bablokb/pcb-pico-pi-base/circuitpython/esp32s3_zero_base_rev1/pins.c

#include "shared-bindings/board/__init__.h"

STATIC const mp_rom_map_elem_t board_module_globals_table[] = {
    CIRCUITPYTHON_BOARD_DICT_STANDARD_ITEMS

    { MP_ROM_QSTR(MP_QSTR_GP0), MP_ROM_PTR(&pin_GPIO11) },
    { MP_ROM_QSTR(MP_QSTR_GP1), MP_ROM_PTR(&pin_GPIO12) },
    { MP_ROM_QSTR(MP_QSTR_GP2), MP_ROM_PTR(&pin_GPIO13) },
    { MP_ROM_QSTR(MP_QSTR_GP3), MP_ROM_PTR(&pin_GPIO14) },
    { MP_ROM_QSTR(MP_QSTR_GP4), MP_ROM_PTR(&pin_GPIO15) },
    { MP_ROM_QSTR(MP_QSTR_GP5), MP_ROM_PTR(&pin_GPIO16) },
    { MP_ROM_QSTR(MP_QSTR_GP6), MP_ROM_PTR(&pin_GPIO17) },
    { MP_ROM_QSTR(MP_QSTR_GP7), MP_ROM_PTR(&pin_GPIO18) },
    { MP_ROM_QSTR(MP_QSTR_GP8), MP_ROM_PTR(&pin_GPIO33) },
    { MP_ROM_QSTR(MP_QSTR_GP9), MP_ROM_PTR(&pin_GPIO34) },
    { MP_ROM_QSTR(MP_QSTR_GP10), MP_ROM_PTR(&pin_GPIO35) },
    { MP_ROM_QSTR(MP_QSTR_GP11), MP_ROM_PTR(&pin_GPIO36) },
    { MP_ROM_QSTR(MP_QSTR_GP12), MP_ROM_PTR(&pin_GPIO37) },
    { MP_ROM_QSTR(MP_QSTR_GP13), MP_ROM_PTR(&pin_GPIO38) },
    { MP_ROM_QSTR(MP_QSTR_GP14), MP_ROM_PTR(&pin_GPIO39) },
    { MP_ROM_QSTR(MP_QSTR_GP15), MP_ROM_PTR(&pin_GPIO40) },
    { MP_ROM_QSTR(MP_QSTR_GP16), MP_ROM_PTR(&pin_GPIO42) },
    { MP_ROM_QSTR(MP_QSTR_GP17), MP_ROM_PTR(&pin_GPIO41) },
    { MP_ROM_QSTR(MP_QSTR_GP18), MP_ROM_PTR(&pin_GPIO1) },
    { MP_ROM_QSTR(MP_QSTR_GP19), MP_ROM_PTR(&pin_GPIO2) },
    { MP_ROM_QSTR(MP_QSTR_GP20), MP_ROM_PTR(&pin_GPIO4) },
    { MP_ROM_QSTR(MP_QSTR_GP21), MP_ROM_PTR(&pin_GPIO5) },
    { MP_ROM_QSTR(MP_QSTR_GP22), MP_ROM_PTR(&pin_GPIO6) },
    { MP_ROM_QSTR(MP_QSTR_GP26), MP_ROM_PTR(&pin_GPIO7) },
    { MP_ROM_QSTR(MP_QSTR_GP27), MP_ROM_PTR(&pin_GPIO8) },
    { MP_ROM_QSTR(MP_QSTR_GP28), MP_ROM_PTR(&pin_GPIO9) },

    { MP_ROM_QSTR(MP_QSTR_GPIO2), MP_ROM_PTR(&pin_GPIO13) },
    { MP_ROM_QSTR(MP_QSTR_SDA),   MP_ROM_PTR(&pin_GPIO13) },

    { MP_ROM_QSTR(MP_QSTR_GPIO3), MP_ROM_PTR(&pin_GPIO14) },
    { MP_ROM_QSTR(MP_QSTR_SCL),   MP_ROM_PTR(&pin_GPIO14) },

    { MP_ROM_QSTR(MP_QSTR_GPIO4), MP_ROM_PTR(&pin_GPIO15) },
    { MP_ROM_QSTR(MP_QSTR_GPIO5), MP_ROM_PTR(&pin_GPIO5) },
    { MP_ROM_QSTR(MP_QSTR_GPIO6), MP_ROM_PTR(&pin_GPIO38) },

    { MP_ROM_QSTR(MP_QSTR_GPIO7), MP_ROM_PTR(&pin_GPIO6) },
    { MP_ROM_QSTR(MP_QSTR_CE1),   MP_ROM_PTR(&pin_GPIO6) },

    { MP_ROM_QSTR(MP_QSTR_GPIO8),  MP_ROM_PTR(&pin_GPIO34) },
    { MP_ROM_QSTR(MP_QSTR_CE0),    MP_ROM_PTR(&pin_GPIO34) },

    { MP_ROM_QSTR(MP_QSTR_GPIO9), MP_ROM_PTR(&pin_GPIO37) },
    { MP_ROM_QSTR(MP_QSTR_MISO),  MP_ROM_PTR(&pin_GPIO37) },

    { MP_ROM_QSTR(MP_QSTR_GPIO10), MP_ROM_PTR(&pin_GPIO36) },
    { MP_ROM_QSTR(MP_QSTR_MOSI),   MP_ROM_PTR(&pin_GPIO36) },

    { MP_ROM_QSTR(MP_QSTR_GPIO11), MP_ROM_PTR(&pin_GPIO35) },
    { MP_ROM_QSTR(MP_QSTR_SCLK),   MP_ROM_PTR(&pin_GPIO35) },

    { MP_ROM_QSTR(MP_QSTR_GPIO12), MP_ROM_PTR(&pin_GPIO4) },
    { MP_ROM_QSTR(MP_QSTR_GPIO13), MP_ROM_PTR(&pin_GPIO39) },

    { MP_ROM_QSTR(MP_QSTR_GPIO14), MP_ROM_PTR(&pin_GPIO11) },
    { MP_ROM_QSTR(MP_QSTR_TX),    MP_ROM_PTR(&pin_GPIO11) },

    { MP_ROM_QSTR(MP_QSTR_GPIO15), MP_ROM_PTR(&pin_GPIO12) },
    { MP_ROM_QSTR(MP_QSTR_RX),     MP_ROM_PTR(&pin_GPIO12) },

    { MP_ROM_QSTR(MP_QSTR_GPIO23), MP_ROM_PTR(&pin_GPIO33) },

    { MP_ROM_QSTR(MP_QSTR_GPIO16), MP_ROM_PTR(&pin_GPIO41) },
    { MP_ROM_QSTR(MP_QSTR_GPIO17), MP_ROM_PTR(&pin_GPIO16) },
    { MP_ROM_QSTR(MP_QSTR_GPIO18), MP_ROM_PTR(&pin_GPIO9) },

    { MP_ROM_QSTR(MP_QSTR_GPIO19), MP_ROM_PTR(&pin_GPIO42) },
    { MP_ROM_QSTR(MP_QSTR_MISO1),  MP_ROM_PTR(&pin_GPIO42) },

    { MP_ROM_QSTR(MP_QSTR_GPIO20), MP_ROM_PTR(&pin_GPIO2) },
    { MP_ROM_QSTR(MP_QSTR_MOSI1),  MP_ROM_PTR(&pin_GPIO2) },

    { MP_ROM_QSTR(MP_QSTR_GPIO21), MP_ROM_PTR(&pin_GPIO1) },
    { MP_ROM_QSTR(MP_QSTR_SCLK1),  MP_ROM_PTR(&pin_GPIO1) },

    { MP_ROM_QSTR(MP_QSTR_GPIO22), MP_ROM_PTR(&pin_GPIO18) },
    { MP_ROM_QSTR(MP_QSTR_GPIO24), MP_ROM_PTR(&pin_GPIO8) },
    { MP_ROM_QSTR(MP_QSTR_GPIO25), MP_ROM_PTR(&pin_GPIO7) },
    { MP_ROM_QSTR(MP_QSTR_GPIO26), MP_ROM_PTR(&pin_GPIO40) },
    { MP_ROM_QSTR(MP_QSTR_GPIO27), MP_ROM_PTR(&pin_GPIO17) },

    { MP_ROM_QSTR(MP_QSTR_NEOPIXEL), MP_ROM_PTR(&pin_GPIO21) },
    { MP_ROM_QSTR(MP_QSTR_VBUS_SENSE), MP_ROM_PTR(&pin_GPIO3) },

    { MP_ROM_QSTR(MP_QSTR_I2C), MP_ROM_PTR(&board_i2c_obj) },
    { MP_ROM_QSTR(MP_QSTR_UART), MP_ROM_PTR(&board_uart_obj) },

};
MP_DEFINE_CONST_DICT(board_module_globals, board_module_globals_table);
